sourya-sen/rPi_synth/rPi_Framework/src/main.cpp

#include "ofMain.h"
#include "ofApp.h"
#include "ofAppNoWindow.h"

//========================================================================
int main( ){
	ofAppNoWindow window;
	ofSetupOpenGL(&window, 1024, 768, OF_WINDOW);
	//ofSetupOpenGL(1024,768,OF_WINDOW);			// <-------- setup the GL context
	ofRunApp(new ofApp());

}
